Terawatt-Industries/x-ends-tw8mmls/img/x_ends_idler_8mmls_acetal.png

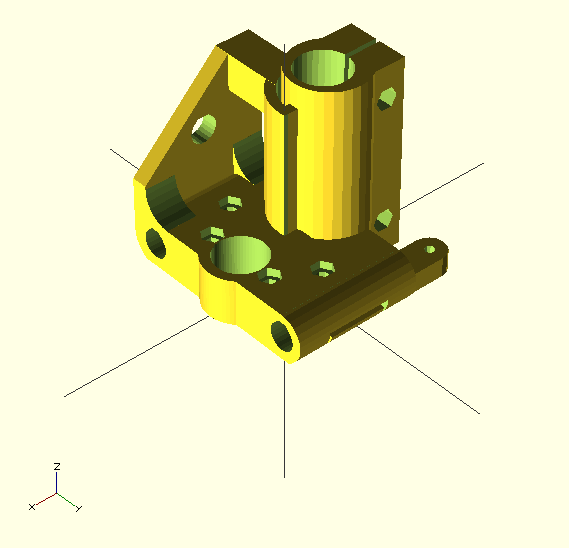
img/x_ends_idler_8mmls_acetal.png
