Terawatt-Industries/x-ends-tw8mmls/img/x_ends_motormount_terawatt_acetal.png

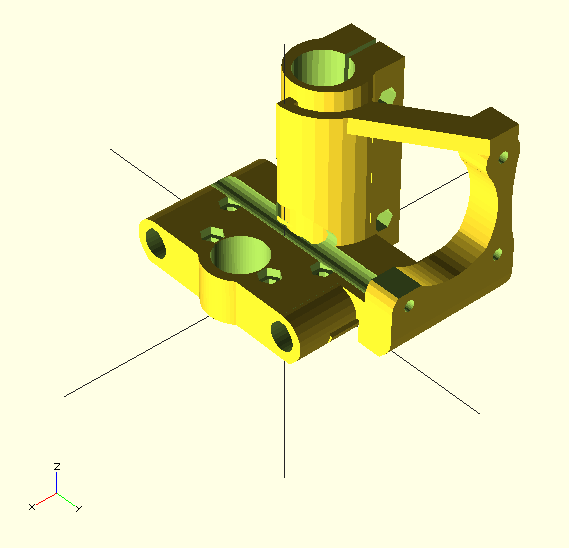
img/x_ends_motormount_terawatt_acetal.png
